Thehi198/embedded-nightlight/docs/nightlight_circuit.kicad_sch

## KiCad design docs/nightlight_circuit.kicad_sch (2026-10-08)

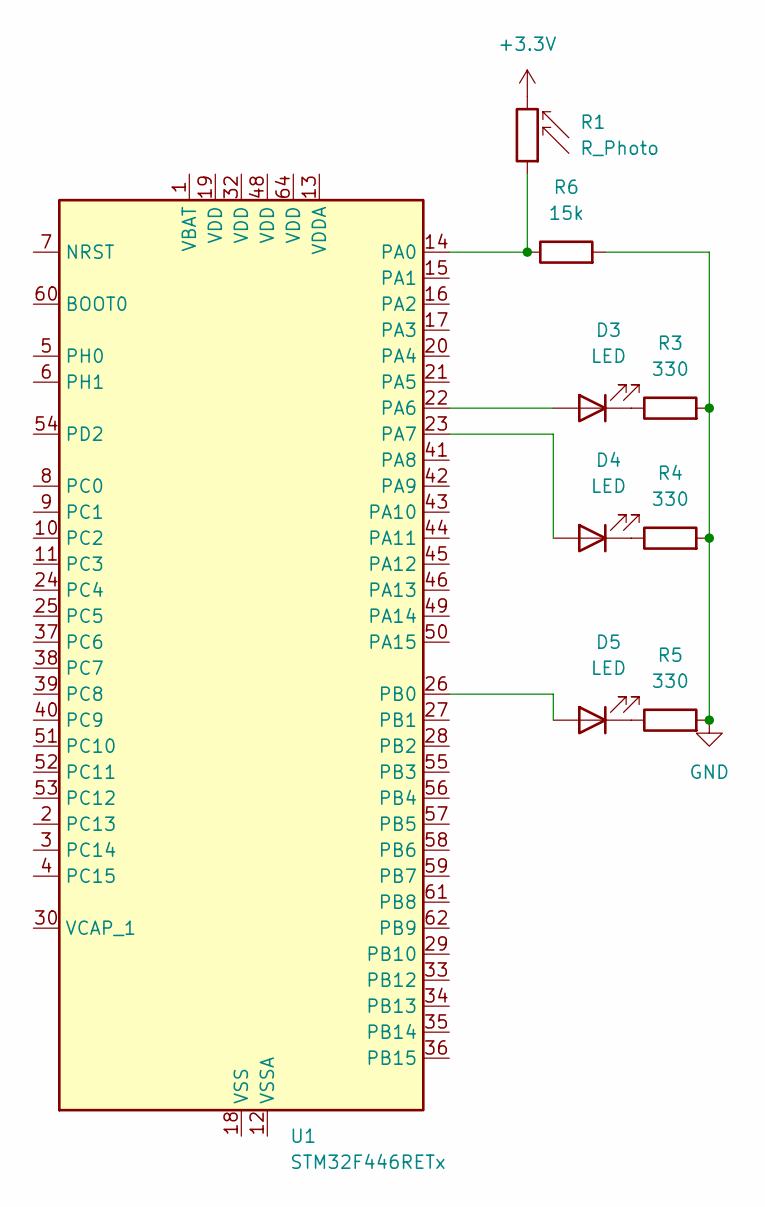
[picture p4: schematic nightlight_circuit.kicad_sch]

Parts:
D3, D4, D5: LED
R1: R_Photo; Toshiba_SOIC-4-6_4.4x3.6mm_P1.27mm
R3, R4, R5: 330; QFN-32-1EP_5x5mm_P0.5mm_EP3.7x3.7mm
R6: 15k; QFN-32-1EP_5x5mm_P0.5mm_EP3.7x3.7mm
U1: STM32F446RETx; LQFP-64_10x10mm_P0.5mm

Connections:
+3.3V: R1.2
GND: R3.2, R4.2, R5.2, R6.2
unnamed: D3.1 (K), R3.1
unnamed: D3.2 (A), U1.22 (PA6)
unnamed: D4.1 (K), R4.1
unnamed: D4.2 (A), U1.23 (PA7)
unnamed: D5.1 (K), R5.1
unnamed: D5.2 (A), U1.26 (PB0)
unnamed: R1.1, R6.1, U1.14 (PA0)
unnamed: U1.18 (VSS), U1.31 (VSS), U1.47 (VSS), U1.63 (VSS)
